alpha-exe-cpu/tkeeb/PCB_KiCad/TKEEB.kicad_sch

## KiCad design PCB_KiCad/TKEEB.kicad_sch (2025-12-29)

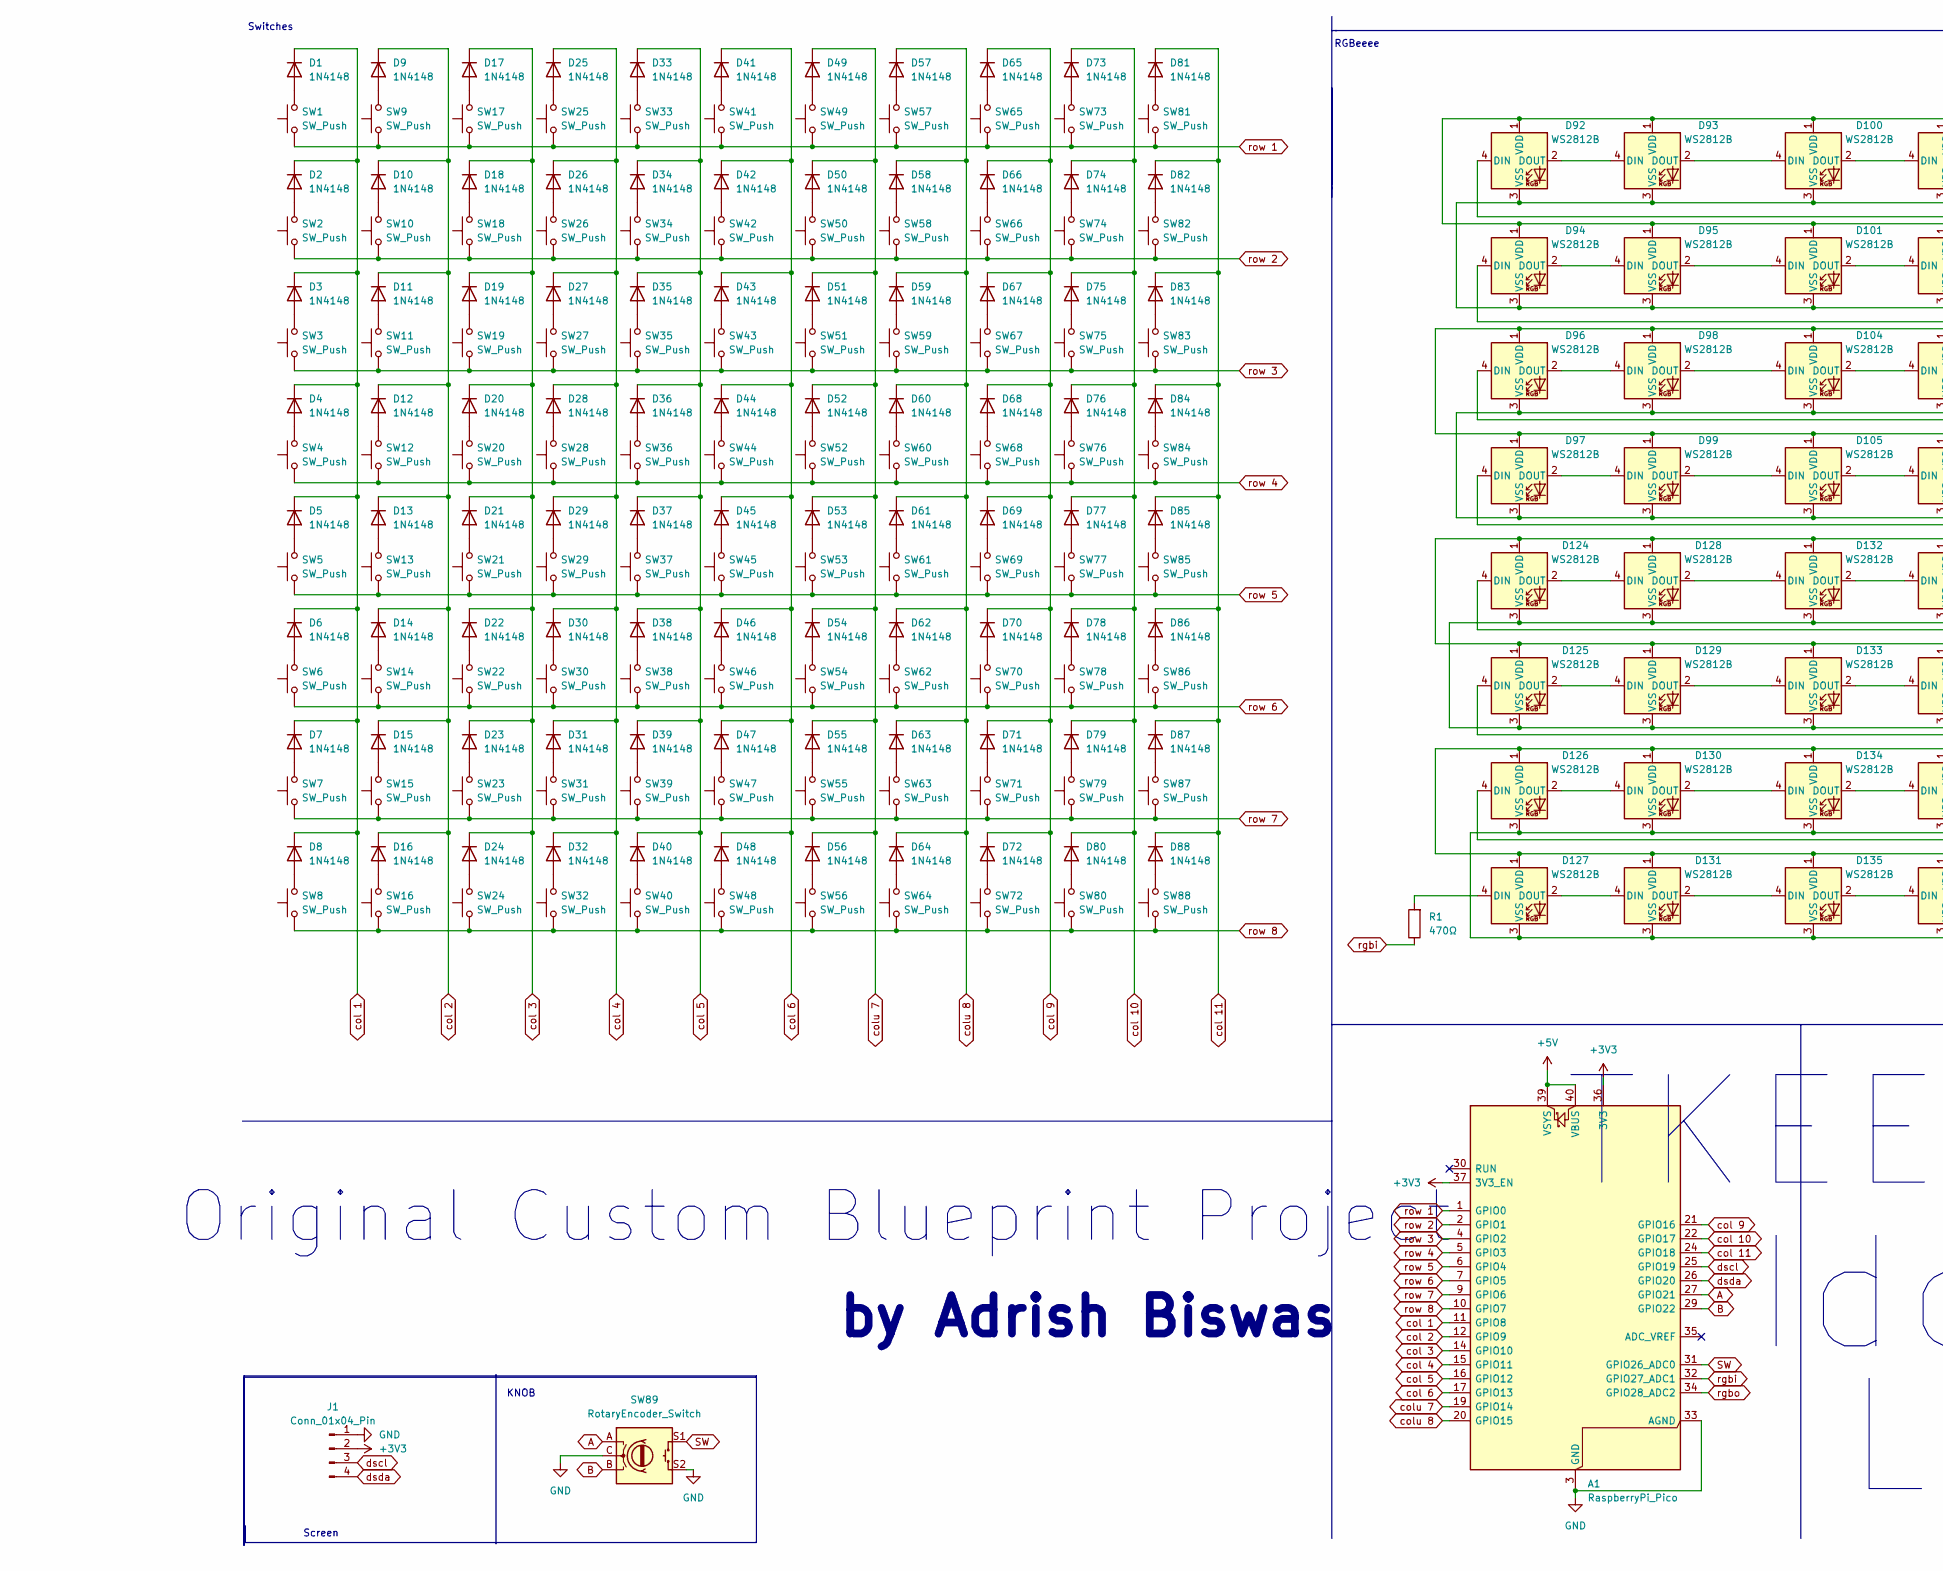
[picture p4: schematic TKEEB.kicad_sch, part in row 1, column 1]

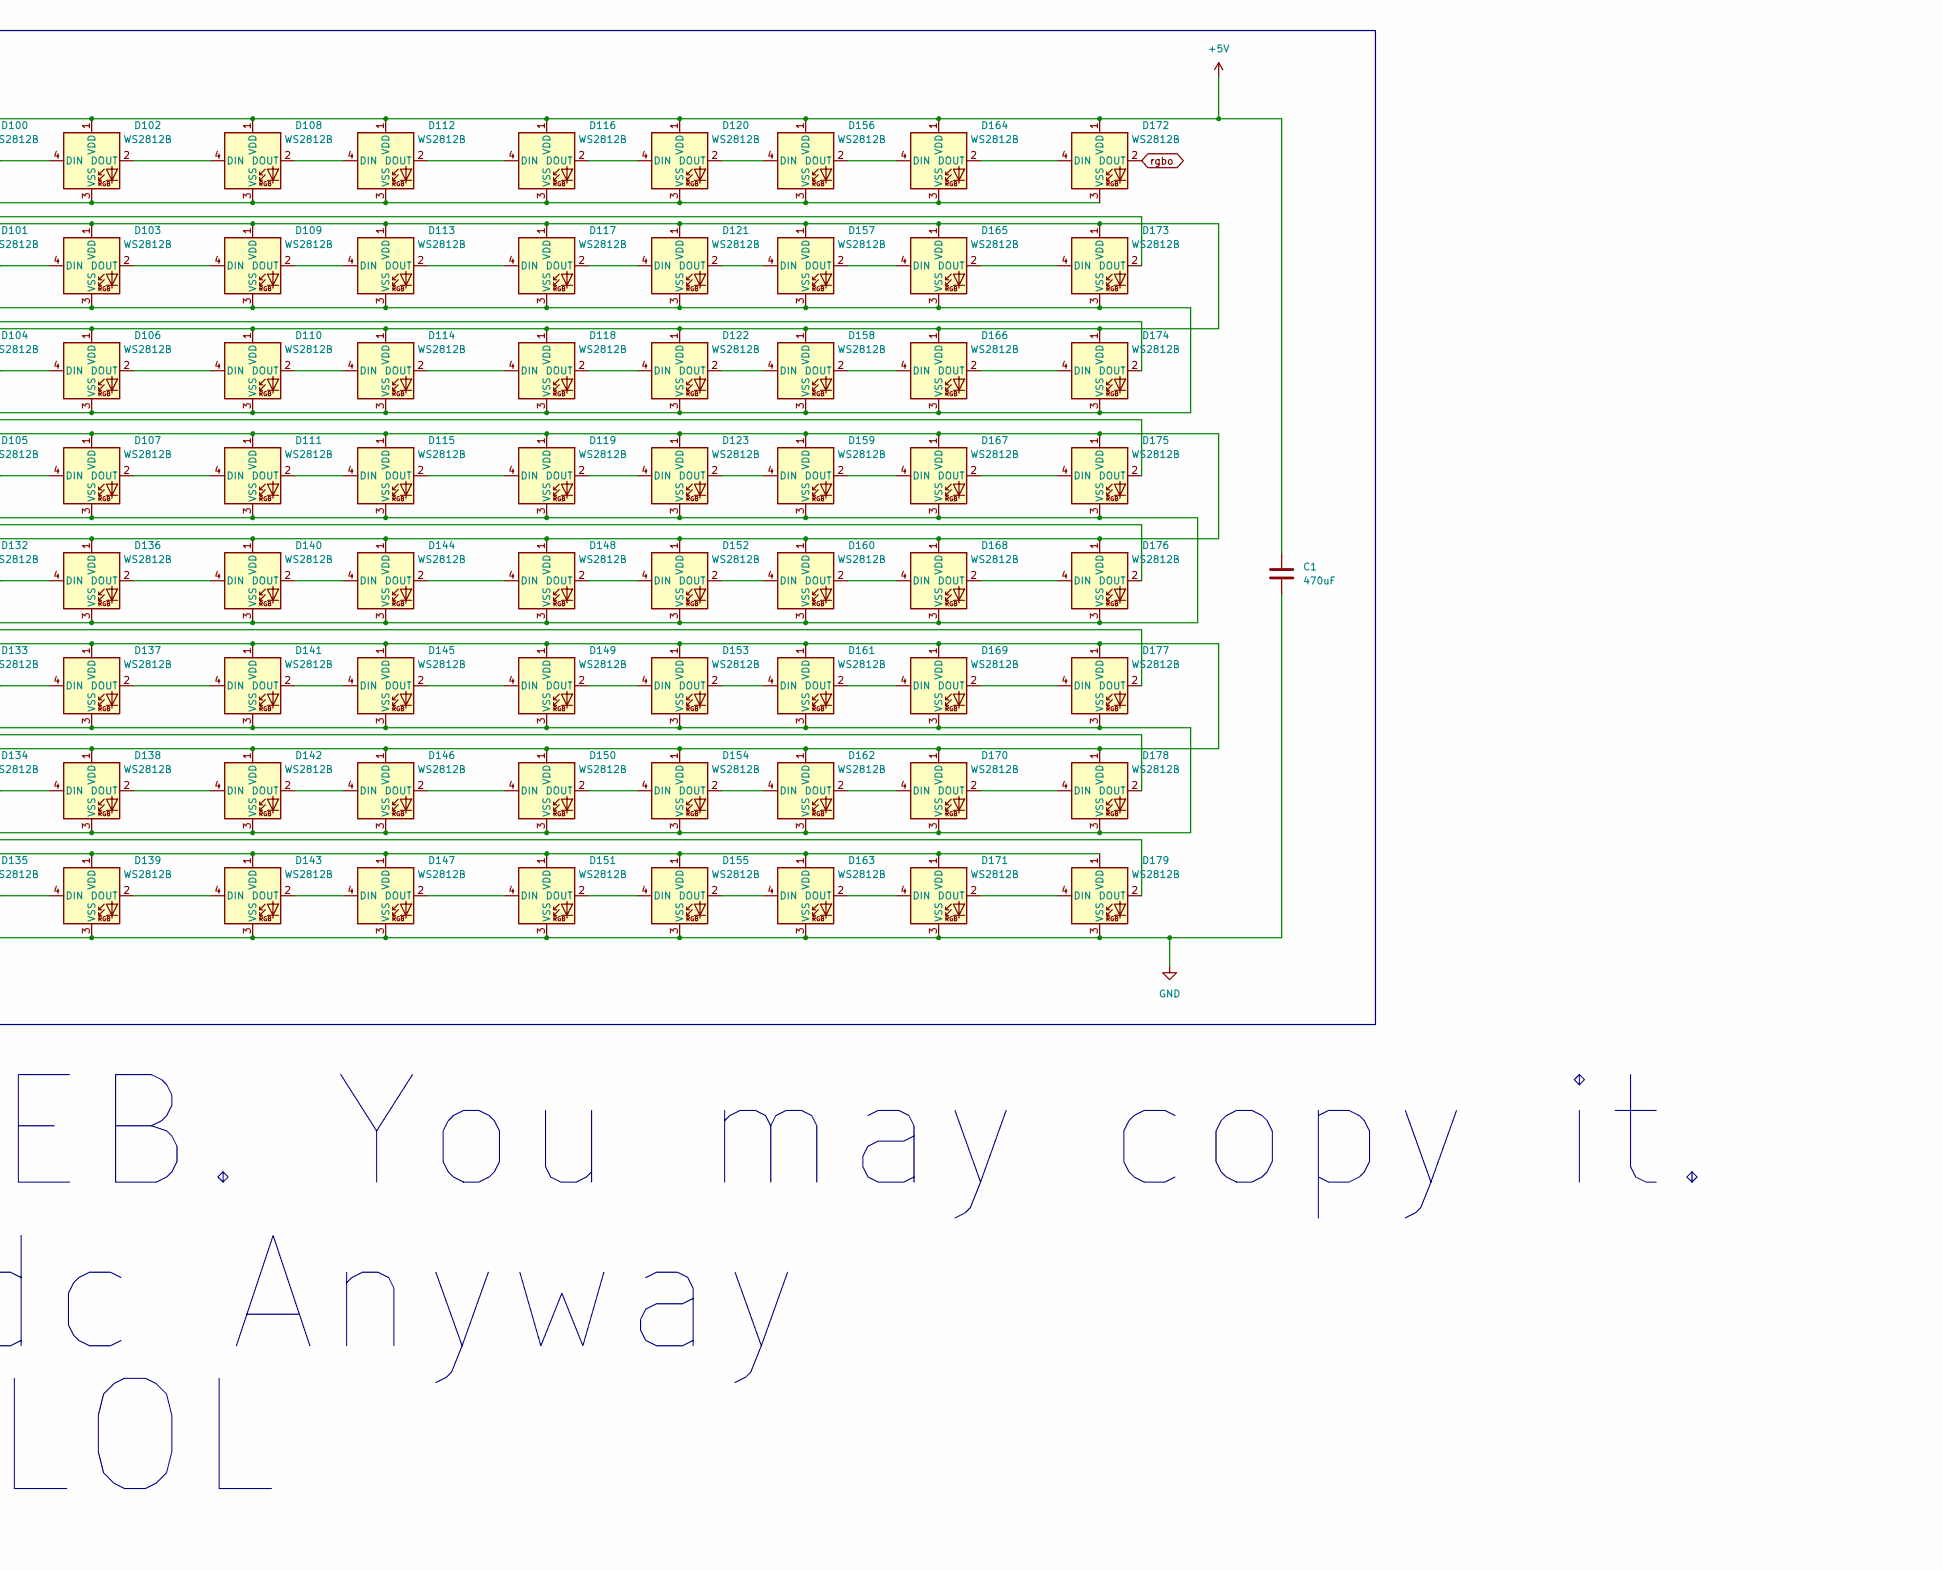
[picture p5: schematic TKEEB.kicad_sch, part in row 1, column 2]

Parts:
A1: RaspberryPi_Pico; RaspberryPi_Pico_Common_Unspecified
C1: 470uF; CP_EIA-7343-31_Kemet-D
D1, D2, D3, D4, D5, D6, D7, D8, D9, D10, D11, D12, D13, D14, D15, D16, D17, D18, D19, D20, D21, D22, D23, D24, D25, D26, D27, D28, D29, D30, D31, D32, D33, D34, D35, D36, D37, D38, D39, D40, D41, D42, D43, D44, D45, D46, D47, D48, D49, D50, D51, D52, D53, D54, D55, D56, D57, D58, D59, D60, D61, D62, D63, D64, D65, D66, D67, D68, D69, D70, D71, D72, D73, D74, D75, D76, D77, D78, D79, D80, D81, D82, D83, D84, D85, D86, D87, D88: 1N4148; D_DO-35_SOD27_P7.62mm_Horizontal
D92, D93, D94, D95, D96, D97, D98, D99, D100, D101, D102, D103, D104, D105, D106, D107, D108, D109, D110, D111, D112, D113, D114, D115, D116, D117, D118, D119, D120, D121, D122, D123, D124, D125, D126, D127, D128, D129, D130, D131, D132, D133, D134, D135, D136, D137, D138, D139, D140, D141, D142, D143, D144, D145, D146, D147, D148, D149, D150, D151, D152, D153, D154, D155, D156, D157, D158, D159, D160, D161, D162, D163, D164, D165, D166, D167, D168, D169, D170, D171, D172, D173, D174, D175, D176, D177, D178, D179: WS2812B; LED_WS2812B_PLCC4_5.0x5.0mm_P3.2mm
J1: Conn_01x04_Pin; SSD1306-0.91-OLED-4pin-128x32
R1: 470Ω; R_0805_2012Metric
SW1, SW2, SW3, SW4, SW5, SW6, SW7, SW8, SW9, SW10, SW11, SW12, SW13, SW14, SW15, SW16, SW17, SW18, SW19, SW20, SW21, SW22, SW23, SW24, SW25, SW26, SW27, SW28, SW29, SW30, SW31, SW32, SW33, SW34, SW35, SW36, SW37, SW38, SW39, SW40, SW41, SW42, SW43, SW44, SW45, SW46, SW47, SW48, SW49, SW50, SW51, SW52, SW53, SW54, SW55, SW56, SW57, SW58, SW59, SW60, SW61, SW62, SW71, SW72, SW73, SW74, SW75, SW76, SW77, SW78, SW79, SW80, SW81: SW_Push; MX-Hotswap-1U
SW63, SW64, SW65, SW67, SW68, SW69, SW70: SW_Push; MX-Hotswap-1.25U
SW66: SW_Push; MX-Hotswap-6.25U
SW82, SW87: SW_Push; MX-Hotswap-2.25U
SW83, SW84: SW_Push; MX-Hotswap-1.5U
SW85: SW_Push; MX-Hotswap-1.75U
SW86: SW_Push; MX-Hotswap-2U
SW88: SW_Push; MX-Hotswap-2.75U
SW89: RotaryEncoder_Switch; RotaryEncoder_Alps_EC11E-Switch_Vertical_H20mm

Connections:
+3V3: A1.36 (3V3), A1.37 (3V3_EN), J1.2
+5V: A1.39 (VSYS), A1.40 (VBUS), C1.1, D92.1 (VDD), D93.1 (VDD), D94.1 (VDD), D95.1 (VDD), D96.1 (VDD), D97.1 (VDD), D98.1 (VDD), D99.1 (VDD), D100.1 (VDD), D101.1 (VDD), D102.1 (VDD), D103.1 (VDD), D104.1 (VDD), D105.1 (VDD), D106.1 (VDD), D107.1 (VDD), D108.1 (VDD), D109.1 (VDD), D110.1 (VDD), D111.1 (VDD), D112.1 (VDD), D113.1 (VDD), D114.1 (VDD), D115.1 (VDD), D116.1 (VDD), D117.1 (VDD), D118.1 (VDD), D119.1 (VDD), D120.1 (VDD), D121.1 (VDD), D122.1 (VDD), D123.1 (VDD), D124.1 (VDD), D125.1 (VDD), D126.1 (VDD), D127.1 (VDD), D128.1 (VDD), D129.1 (VDD), D130.1 (VDD), D131.1 (VDD), D132.1 (VDD), D133.1 (VDD), D134.1 (VDD), D135.1 (VDD), D136.1 (VDD), D137.1 (VDD), D138.1 (VDD), D139.1 (VDD), D140.1 (VDD), D141.1 (VDD), D142.1 (VDD), D143.1 (VDD), D144.1 (VDD), D145.1 (VDD), D146.1 (VDD), D147.1 (VDD), D148.1 (VDD), D149.1 (VDD), D150.1 (VDD), D151.1 (VDD), D152.1 (VDD), D153.1 (VDD), D154.1 (VDD), D155.1 (VDD), D156.1 (VDD), D157.1 (VDD), D158.1 (VDD), D159.1 (VDD), D160.1 (VDD), D161.1 (VDD), D162.1 (VDD), D163.1 (VDD), D164.1 (VDD), D165.1 (VDD), D166.1 (VDD), D167.1 (VDD), D168.1 (VDD), D169.1 (VDD), D170.1 (VDD), D171.1 (VDD), D172.1 (VDD), D173.1 (VDD), D174.1 (VDD), D175.1 (VDD), D176.1 (VDD), D177.1 (VDD), D178.1 (VDD), D179.1 (VDD)
A: A1.27 (GPIO21), SW89.A
B: A1.29 (GPIO22), SW89.B
GND: A1.3 (GND), A1.8 (GND), A1.13 (GND), A1.18 (GND), A1.23 (GND), A1.28 (GND), A1.33 (AGND), A1.38 (GND), C1.2, D92.3 (VSS), D93.3 (VSS), D94.3 (VSS), D95.3 (VSS), D96.3 (VSS), D97.3 (VSS), D98.3 (VSS), D99.3 (VSS), D100.3 (VSS), D101.3 (VSS), D102.3 (VSS), D103.3 (VSS), D104.3 (VSS), D105.3 (VSS), D106.3 (VSS), D107.3 (VSS), D108.3 (VSS), D109.3 (VSS), D110.3 (VSS), D111.3 (VSS), D112.3 (VSS), D113.3 (VSS), D114.3 (VSS), D115.3 (VSS), D116.3 (VSS), D117.3 (VSS), D118.3 (VSS), D119.3 (VSS), D120.3 (VSS), D121.3 (VSS), D122.3 (VSS), D123.3 (VSS), D124.3 (VSS), D125.3 (VSS), D126.3 (VSS), D127.3 (VSS), D128.3 (VSS), D129.3 (VSS), D130.3 (VSS), D131.3 (VSS), D132.3 (VSS), D133.3 (VSS), D134.3 (VSS), D135.3 (VSS), D136.3 (VSS), D137.3 (VSS), D138.3 (VSS), D139.3 (VSS), D140.3 (VSS), D141.3 (VSS), D142.3 (VSS), D143.3 (VSS), D144.3 (VSS), D145.3 (VSS), D146.3 (VSS), D147.3 (VSS), D148.3 (VSS), D149.3 (VSS), D150.3 (VSS), D151.3 (VSS), D152.3 (VSS), D153.3 (VSS), D154.3 (VSS), D155.3 (VSS), D156.3 (VSS), D157.3 (VSS), D158.3 (VSS), D159.3 (VSS), D160.3 (VSS), D161.3 (VSS), D162.3 (VSS), D163.3 (VSS), D164.3 (VSS), D165.3 (VSS), D166.3 (VSS), D167.3 (VSS), D168.3 (VSS), D169.3 (VSS), D170.3 (VSS), D171.3 (VSS), D172.3 (VSS), D173.3 (VSS), D174.3 (VSS), D175.3 (VSS), D176.3 (VSS), D177.3 (VSS), D178.3 (VSS), D179.3 (VSS), J1.1, SW89.C, SW89.S2
unnamed: D1.2 (A), SW1.2
unnamed: D2.2 (A), SW2.2
unnamed: D3.2 (A), SW3.2
unnamed: D4.2 (A), SW4.2
unnamed: D5.2 (A), SW5.2
unnamed: D6.2 (A), SW6.2
unnamed: D7.2 (A), SW7.2
unnamed: D8.2 (A), SW8.2
unnamed: D9.2 (A), SW9.2
unnamed: D10.2 (A), SW10.2
unnamed: D11.2 (A), SW11.2
unnamed: D12.2 (A), SW12.2
unnamed: D13.2 (A), SW13.2
unnamed: D14.2 (A), SW14.2
unnamed: D15.2 (A), SW15.2
unnamed: D16.2 (A), SW16.2
unnamed: D17.2 (A), SW17.2
unnamed: D18.2 (A), SW18.2
unnamed: D19.2 (A), SW19.2
unnamed: D20.2 (A), SW20.2
unnamed: D21.2 (A), SW21.2
unnamed: D22.2 (A), SW22.2
unnamed: D23.2 (A), SW23.2
unnamed: D24.2 (A), SW24.2
unnamed: D25.2 (A), SW25.2
unnamed: D26.2 (A), SW26.2
unnamed: D27.2 (A), SW27.2
unnamed: D28.2 (A), SW28.2
unnamed: D29.2 (A), SW29.2
unnamed: D30.2 (A), SW30.2
unnamed: D31.2 (A), SW31.2
unnamed: D32.2 (A), SW32.2
unnamed: D33.2 (A), SW33.2
unnamed: D34.2 (A), SW34.2
unnamed: D35.2 (A), SW35.2
unnamed: D36.2 (A), SW36.2
unnamed: D37.2 (A), SW37.2
unnamed: D38.2 (A), SW38.2
unnamed: D39.2 (A), SW39.2
unnamed: D40.2 (A), SW40.2
unnamed: D41.2 (A), SW41.2
unnamed: D42.2 (A), SW42.2
unnamed: D43.2 (A), SW43.2
unnamed: D44.2 (A), SW44.2
unnamed: D45.2 (A), SW45.2
unnamed: D46.2 (A), SW46.2
unnamed: D47.2 (A), SW47.2
unnamed: D48.2 (A), SW48.2
unnamed: D49.2 (A), SW49.2
unnamed: D50.2 (A), SW50.2
unnamed: D51.2 (A), SW51.2
unnamed: D52.2 (A), SW52.2
unnamed: D53.2 (A), SW53.2
unnamed: D54.2 (A), SW54.2
unnamed: D55.2 (A), SW55.2
unnamed: D56.2 (A), SW56.2
unnamed: D57.2 (A), SW57.2
unnamed: D58.2 (A), SW58.2
unnamed: D59.2 (A), SW59.2
unnamed: D60.2 (A), SW60.2
unnamed: D61.2 (A), SW61.2
unnamed: D62.2 (A), SW62.2
unnamed: D63.2 (A), SW63.2
unnamed: D64.2 (A), SW64.2
unnamed: D65.2 (A), SW65.2
unnamed: D66.2 (A), SW66.2
unnamed: D67.2 (A), SW67.2
unnamed: D68.2 (A), SW68.2
unnamed: D69.2 (A), SW69.2
unnamed: D70.2 (A), SW70.2
unnamed: D71.2 (A), SW71.2
unnamed: D72.2 (A), SW72.2
unnamed: D73.2 (A), SW73.2
unnamed: D74.2 (A), SW74.2
unnamed: D75.2 (A), SW75.2
unnamed: D76.2 (A), SW76.2
unnamed: D77.2 (A), SW77.2
unnamed: D78.2 (A), SW78.2
unnamed: D79.2 (A), SW79.2
unnamed: D80.2 (A), SW80.2
unnamed: D81.2 (A), SW81.2
unnamed: D82.2 (A), SW82.2
unnamed: D83.2 (A), SW83.2
unnamed: D84.2 (A), SW84.2
unnamed: D85.2 (A), SW85.2
unnamed: D86.2 (A), SW86.2
unnamed: D87.2 (A), SW87.2
unnamed: D88.2 (A), SW88.2
unnamed: D92.2 (DOUT), D93.4 (DIN)
unnamed: D94.2 (DOUT), D95.4 (DIN)
unnamed: D96.2 (DOUT), D98.4 (DIN)
unnamed: D97.2 (DOUT), D99.4 (DIN)
unnamed: D100.2 (DOUT), D102.4 (DIN)
unnamed: D93.2 (DOUT), D100.4 (DIN)
unnamed: D101.2 (DOUT), D103.4 (DIN)
unnamed: D95.2 (DOUT), D101.4 (DIN)
unnamed: D102.2 (DOUT), D108.4 (DIN)
unnamed: D103.2 (DOUT), D109.4 (DIN)
unnamed: D104.2 (DOUT), D106.4 (DIN)
unnamed: D98.2 (DOUT), D104.4 (DIN)
unnamed: D105.2 (DOUT), D107.4 (DIN)
unnamed: D99.2 (DOUT), D105.4 (DIN)
unnamed: D106.2 (DOUT), D110.4 (DIN)
unnamed: D107.2 (DOUT), D111.4 (DIN)
unnamed: D108.2 (DOUT), D112.4 (DIN)
unnamed: D109.2 (DOUT), D113.4 (DIN)
unnamed: D110.2 (DOUT), D114.4 (DIN)
unnamed: D111.2 (DOUT), D115.4 (DIN)
unnamed: D112.2 (DOUT), D116.4 (DIN)
unnamed: D113.2 (DOUT), D117.4 (DIN)
unnamed: D114.2 (DOUT), D118.4 (DIN)
unnamed: D115.2 (DOUT), D119.4 (DIN)
unnamed: D116.2 (DOUT), D120.4 (DIN)
unnamed: D117.2 (DOUT), D121.4 (DIN)
unnamed: D118.2 (DOUT), D122.4 (DIN)
unnamed: D119.2 (DOUT), D123.4 (DIN)
unnamed: D120.2 (DOUT), D156.4 (DIN)
unnamed: D121.2 (DOUT), D157.4 (DIN)
unnamed: D122.2 (DOUT), D158.4 (DIN)
unnamed: D123.2 (DOUT), D159.4 (DIN)
unnamed: D124.2 (DOUT), D128.4 (DIN)
unnamed: D124.4 (DIN), D177.2 (DOUT)
unnamed: D125.2 (DOUT), D129.4 (DIN)
unnamed: D125.4 (DIN), D178.2 (DOUT)
unnamed: D126.2 (DOUT), D130.4 (DIN)
unnamed: D126.4 (DIN), D179.2 (DOUT)
unnamed: D127.2 (DOUT), D131.4 (DIN)
unnamed: D127.4 (DIN), R1.2
unnamed: D128.2 (DOUT), D132.4 (DIN)
unnamed: D129.2 (DOUT), D133.4 (DIN)
unnamed: D130.2 (DOUT), D134.4 (DIN)
unnamed: D131.2 (DOUT), D135.4 (DIN)
unnamed: D132.2 (DOUT), D136.4 (DIN)
unnamed: D133.2 (DOUT), D137.4 (DIN)
unnamed: D134.2 (DOUT), D138.4 (DIN)
unnamed: D135.2 (DOUT), D139.4 (DIN)
unnamed: D136.2 (DOUT), D140.4 (DIN)
unnamed: D137.2 (DOUT), D141.4 (DIN)
unnamed: D138.2 (DOUT), D142.4 (DIN)
unnamed: D139.2 (DOUT), D143.4 (DIN)
unnamed: D140.2 (DOUT), D144.4 (DIN)
unnamed: D141.2 (DOUT), D145.4 (DIN)
unnamed: D142.2 (DOUT), D146.4 (DIN)
unnamed: D143.2 (DOUT), D147.4 (DIN)
unnamed: D144.2 (DOUT), D148.4 (DIN)
unnamed: D145.2 (DOUT), D149.4 (DIN)
unnamed: D146.2 (DOUT), D150.4 (DIN)
unnamed: D147.2 (DOUT), D151.4 (DIN)
unnamed: D148.2 (DOUT), D152.4 (DIN)
unnamed: D149.2 (DOUT), D153.4 (DIN)
unnamed: D150.2 (DOUT), D154.4 (DIN)
unnamed: D151.2 (DOUT), D155.4 (DIN)
unnamed: D152.2 (DOUT), D160.4 (DIN)
unnamed: D153.2 (DOUT), D161.4 (DIN)
unnamed: D154.2 (DOUT), D162.4 (DIN)
unnamed: D155.2 (DOUT), D163.4 (DIN)
unnamed: D156.2 (DOUT), D164.4 (DIN)
unnamed: D157.2 (DOUT), D165.4 (DIN)
unnamed: D158.2 (DOUT), D166.4 (DIN)
unnamed: D159.2 (DOUT), D167.4 (DIN)
unnamed: D160.2 (DOUT), D168.4 (DIN)
unnamed: D161.2 (DOUT), D169.4 (DIN)
unnamed: D162.2 (DOUT), D170.4 (DIN)
unnamed: D163.2 (DOUT), D171.4 (DIN)
unnamed: D164.2 (DOUT), D172.4 (DIN)
unnamed: D165.2 (DOUT), D173.4 (DIN)
unnamed: D166.2 (DOUT), D174.4 (DIN)
unnamed: D167.2 (DOUT), D175.4 (DIN)
unnamed: D168.2 (DOUT), D176.4 (DIN)
unnamed: D169.2 (DOUT), D177.4 (DIN)
unnamed: D170.2 (DOUT), D178.4 (DIN)
unnamed: D171.2 (DOUT), D179.4 (DIN)
unnamed: D92.4 (DIN), D173.2 (DOUT)
unnamed: D94.4 (DIN), D174.2 (DOUT)
unnamed: D96.4 (DIN), D175.2 (DOUT)
unnamed: D97.4 (DIN), D176.2 (DOUT)
SW: A1.31 (GPIO26_ADC0), SW89.S1
col 1: A1.11 (GPIO8), D1.1 (K), D2.1 (K), D3.1 (K), D4.1 (K), D5.1 (K), D6.1 (K), D7.1 (K), D8.1 (K)
col 2: A1.12 (GPIO9), D9.1 (K), D10.1 (K), D11.1 (K), D12.1 (K), D13.1 (K), D14.1 (K), D15.1 (K), D16.1 (K)
col 3: A1.14 (GPIO10), D17.1 (K), D18.1 (K), D19.1 (K), D20.1 (K), D21.1 (K), D22.1 (K), D23.1 (K), D24.1 (K)
col 4: A1.15 (GPIO11), D25.1 (K), D26.1 (K), D27.1 (K), D28.1 (K), D29.1 (K), D30.1 (K), D31.1 (K), D32.1 (K)
col 5: A1.16 (GPIO12), D33.1 (K), D34.1 (K), D35.1 (K), D36.1 (K), D37.1 (K), D38.1 (K), D39.1 (K), D40.1 (K)
col 6: A1.17 (GPIO13), D41.1 (K), D42.1 (K), D43.1 (K), D44.1 (K), D45.1 (K), D46.1 (K), D47.1 (K), D48.1 (K)
col 9: A1.21 (GPIO16), D65.1 (K), D66.1 (K), D67.1 (K), D68.1 (K), D69.1 (K), D70.1 (K), D71.1 (K), D72.1 (K)
col 10: A1.22 (GPIO17), D73.1 (K), D74.1 (K), D75.1 (K), D76.1 (K), D77.1 (K), D78.1 (K), D79.1 (K), D80.1 (K)
col 11: A1.24 (GPIO18), D81.1 (K), D82.1 (K), D83.1 (K), D84.1 (K), D85.1 (K), D86.1 (K), D87.1 (K), D88.1 (K)
colu 7: A1.19 (GPIO14), D49.1 (K), D50.1 (K), D51.1 (K), D52.1 (K), D53.1 (K), D54.1 (K), D55.1 (K), D56.1 (K)
colu 8: A1.20 (GPIO15), D57.1 (K), D58.1 (K), D59.1 (K), D60.1 (K), D61.1 (K), D62.1 (K), D63.1 (K), D64.1 (K)
dscl: A1.25 (GPIO19), J1.3
dsda: A1.26 (GPIO20), J1.4
rgbi: A1.32 (GPIO27_ADC1), R1.1
rgbo: A1.34 (GPIO28_ADC2), D172.2 (DOUT)
row 1: A1.1 (GPIO0), SW1.1, SW9.1, SW17.1, SW25.1, SW33.1, SW41.1, SW49.1, SW57.1, SW65.1, SW73.1, SW81.1
row 2: A1.2 (GPIO1), SW2.1, SW10.1, SW18.1, SW26.1, SW34.1, SW42.1, SW50.1, SW58.1, SW66.1, SW74.1, SW82.1
row 3: A1.4 (GPIO2), SW3.1, SW11.1, SW19.1, SW27.1, SW35.1, SW43.1, SW51.1, SW59.1, SW67.1, SW75.1, SW83.1
row 4: A1.5 (GPIO3), SW4.1, SW12.1, SW20.1, SW28.1, SW36.1, SW44.1, SW52.1, SW60.1, SW68.1, SW76.1, SW84.1
row 5: A1.6 (GPIO4), SW5.1, SW13.1, SW21.1, SW29.1, SW37.1, SW45.1, SW53.1, SW61.1, SW69.1, SW77.1, SW85.1
row 6: A1.7 (GPIO5), SW6.1, SW14.1, SW22.1, SW30.1, SW38.1, SW46.1, SW54.1, SW62.1, SW70.1, SW78.1, SW86.1
row 7: A1.9 (GPIO6), SW7.1, SW15.1, SW23.1, SW31.1, SW39.1, SW47.1, SW55.1, SW63.1, SW71.1, SW79.1, SW87.1
row 8: A1.10 (GPIO7), SW8.1, SW16.1, SW24.1, SW32.1, SW40.1, SW48.1, SW56.1, SW64.1, SW72.1, SW80.1, SW88.1

Notes on the sheet:
Screen
LOL
Original Custom Blueprint Project
TKEEB. You may copy it.
Idc Anyway
by Adrish Biswas
KNOB
RGBeeee
Switches
